bonitoo-io/weather-station/arduino/WeatherStation/WeatherStationImages.h

#define Logo_width 52
#define Logo_height 60
const uint8_t Logo_XBM [] PROGMEM = {
 0x00,0x00,0xe0,0x00,0x00,0x00,0xf0,0x00,0x00,0xf8,0x07,0x00,
 0x00,0xf0,0x00,0x00,0xfc,0x7f,0x00,0x00,0xf0,0x00,0x00,0xfe,
 0xff,0x03,0x00,0xf0,0x00,0x00,0xff,0xff,0x1f,0x00,0xf0,0x00,
 0x80,0x9f,0xfd,0xff,0x00,0xf0,0x00,0xc0,0x0f,0xc3,0xff,0x07,
 0xf0,0x00,0xe0,0x07,0x06,0xfe,0x1f,0xf0,0x00,0xf0,0x03,0x0c,
 0xf0,0x1f,0xf0,0x00,0xf8,0x01,0x18,0xc0,0x1f,0xf0,0x00,0x7c,
 0x00,0x30,0xfc,0x3f,0xf0,0x00,0x3f,0x00,0xe0,0x0f,0x3c,0xf0,
 0x80,0x1f,0x00,0xf0,0x00,0x3c,0xf0,0xc0,0x0f,0x00,0x78,0x00,
 0x3c,0xf0,0xe0,0x07,0x00,0xd8,0x00,0x3c,0xf0,0xe0,0x03,0x00,
 0xce,0x00,0x7c,0xf0,0xe0,0x01,0x00,0xc7,0x00,0x78,0xf0,0xe0,
 0x03,0x80,0x81,0x00,0x78,0xf0,0xe0,0x07,0xc0,0x80,0x00,0x78,
 0xf0,0xe0,0x0f,0x60,0x80,0x01,0xf8,0xf0,0xe0,0x1b,0x30,0x80,
 0x01,0xf0,0xf0,0xc0,0x3b,0x18,0x00,0x01,0xf0,0xf0,0xc0,0x63,
 0x0c,0x00,0x01,0xf0,0xf0,0xc0,0x63,0x06,0x00,0x03,0xf0,0xf1,
 0xc0,0xc7,0x03,0x00,0x03,0xf0,0xf1,0x80,0x87,0x0f,0x00,0x03,
 0xe0,0xf1,0x80,0x87,0x7f,0x00,0x02,0xe0,0xf1,0x80,0xc7,0xe0,
 0x03,0x06,0xe0,0xf1,0x80,0xcf,0x00,0x3f,0x06,0xfe,0xf1,0x00,
 0xcf,0x00,0xf8,0xe7,0xff,0xf1,0x00,0x4f,0x00,0x80,0xff,0xf9,
 0xf1,0x00,0x6f,0x00,0x00,0x0e,0xfc,0xf0,0x00,0x6f,0x00,0x00,
 0x06,0x7e,0xf0,0x00,0x3f,0x00,0x00,0x86,0x1f,0xf0,0x00,0x3e,
 0x00,0x00,0xc2,0x0f,0xf0,0x00,0x3e,0x00,0x00,0xe3,0x07,0xf0,
 0x00,0x7e,0x00,0x00,0xf3,0x03,0xf0,0x00,0xfe,0x03,0x00,0xf9,
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
  0x00, 0x76, 0x00, 0xF0, 0xFF, 0xFF, 0x3F, 0x00, 0xE0, 0xFF, 0xFF, 0x1F,
  0x00, 0xC0, 0x03, 0x00, 0x0F, 0x00, 0x80, 0x07, 0xC0, 0x07, 0x00, 0x00,
  0xFF, 0xFF, 0x01, 0x00, 0x00, 0xFC, 0x7F, 0x00, 0x00, 0x00, 0xC0, 0x0F,
  0x00, 0x00, };
